joeyparrish/retcon/circuit/nintendo.brd.png

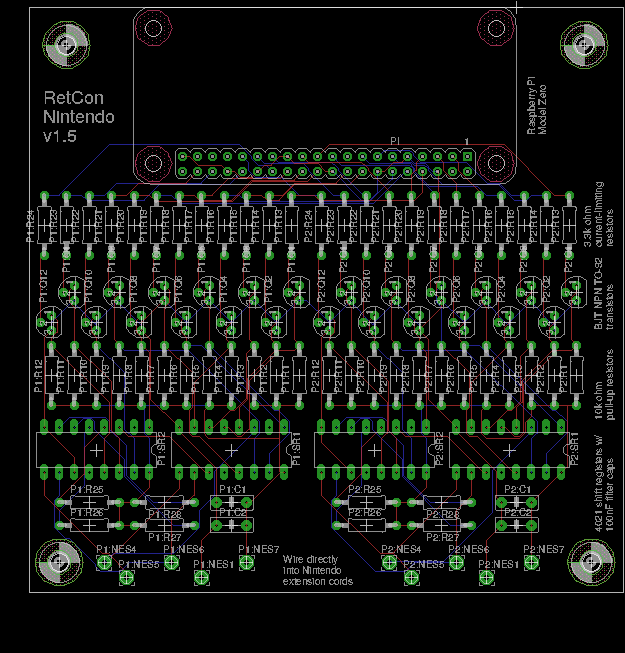
circuit/nintendo.brd.png
