joeyparrish/retcon/circuit/nintendo.sch.1.png

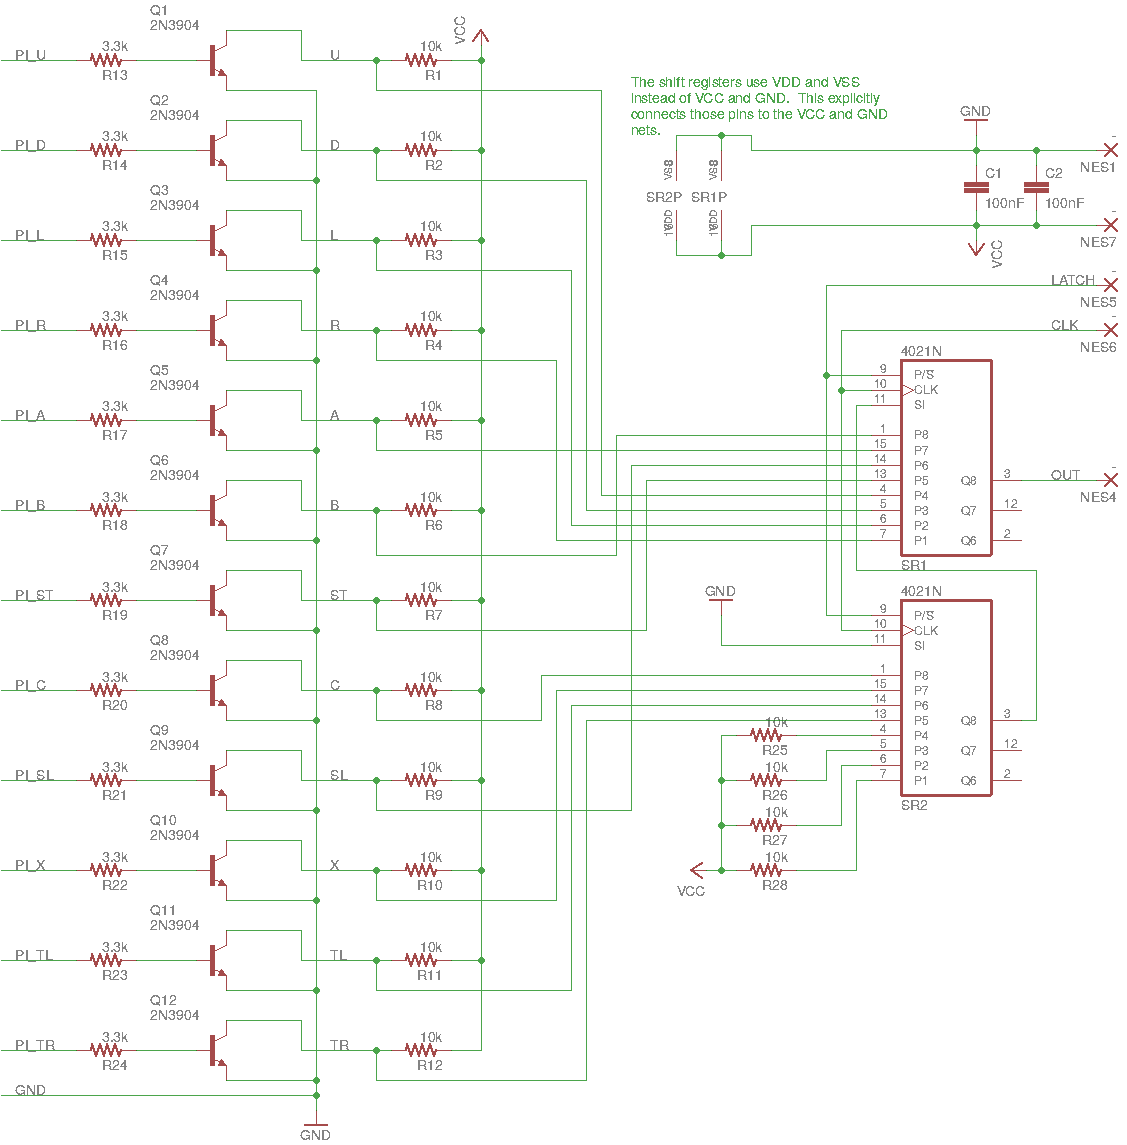
circuit/nintendo.sch.1.png
