joeyparrish/retcon/circuit/nintendo.sch.2.png

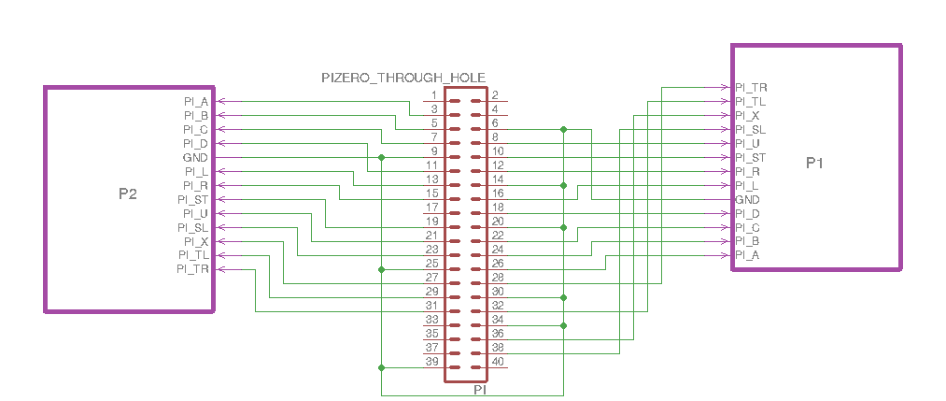
circuit/nintendo.sch.2.png
