joeyparrish/retcon/circuit/sega.sch.1.png

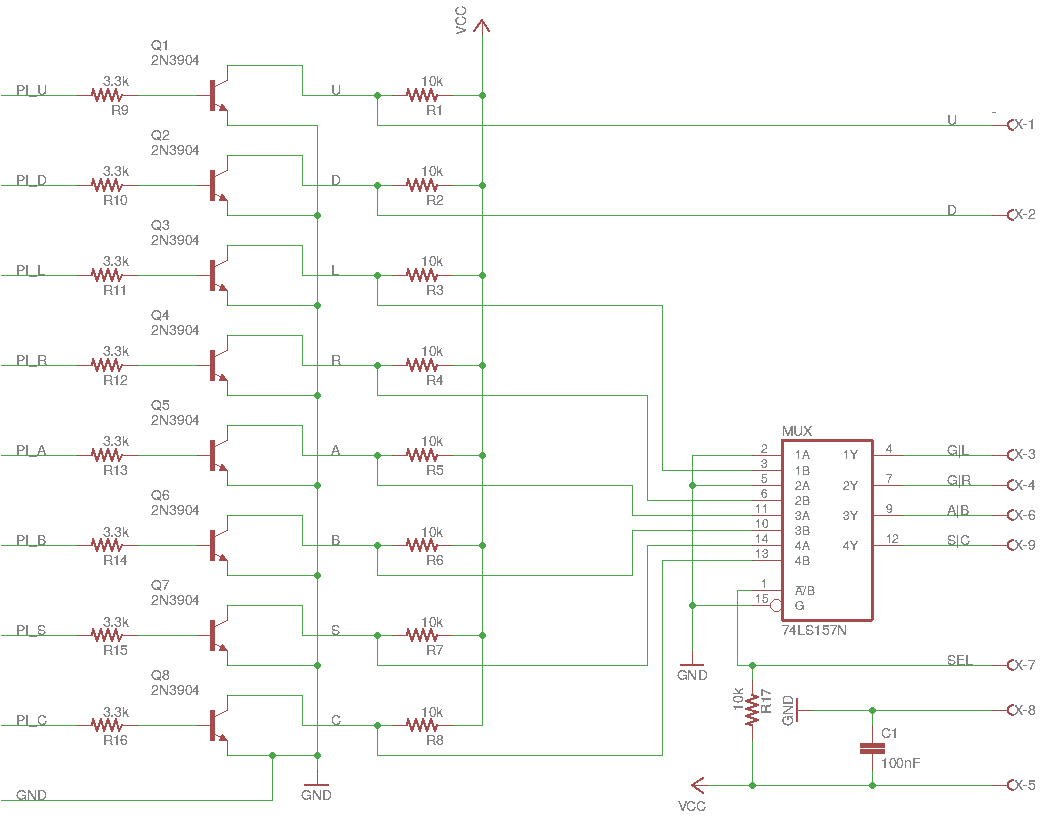
circuit/sega.sch.1.png
